zeroflow/wifi-fancontroller/modules/usr_buttons_mode.yaml

# USR Buttons Fan Control Module with Auto/Manual Mode
#
# Physical button control for fan speed using the 3 USR buttons and per-fan RGB LEDs.
# Requires Rev 3.1+ boards (which have per-fan RGB LEDs for visual feedback).
#
# Button functions (top to bottom on board):
#   USR1 (speed up): Increases selected fan speed by speed_step%. Turns fan on if off.
#                    Clamps to safety floor if stall_guard is active.
#   USR2 (select): Cycles fan selection (1→2→3→4→1). First press enters selection mode.
#                  The selected fan's LED shows that fan's current mode: magenta if it
#                  is in manual, selection_color if it is under automatic control. The
#                  other three LEDs turn off.
#   USR2 (hold ~1s): Toggles the currently selected fan between automatic
#                  temperature control and manual control. The fan stays
#                  selected and the selection window restarts, so USR1 and
#                  USR3 can set its speed right away; the LEDs return to the
#                  selection display after the confirmation flash. The
#                  toggle never changes the fan's commanded speed.
#   USR3 (speed down): Decreases selected fan speed by speed_step%. Turns fan off at 0%.
#
# Manual speed overrides persist until cleared via HA entities or the clear button.
# Selection mode auto-deactivates after override_timeout with no button presses.
#
# Coordinates with rpm_status_leds via auto_led_override global (defined in globals.yaml).
# Coordinates with temperature modules via usr_override_fan{N} globals (defined in globals.yaml).
# Respects fan{N}_safety_floor globals (defined in globals.yaml, written by stall_guard).
#
# Requires globals.yaml to be included (via hardware package or directly).
#
# SUPERSET OF usr_buttons.yaml. This module does everything usr_buttons.yaml
# does (fan selection, speed up/down, LED feedback, the four per-fan manual
# override switches) and adds the USR2 long-press mode toggle above. It
# defines the same component ids as usr_buttons.yaml. Load one or the other,
# never both.
#
# Usage:
#   packages:
#     usr_buttons_mode:
#       url: https://github.com/zeroflow/wifi-fancontroller
#       ref: main
#       files:
#         - path: modules/usr_buttons_mode.yaml
#           vars:
#             friendly_name: "My Fan Controller"
#             speed_step: "10"
#             override_timeout: "30s"
#             selection_color_r: "0"
#             selection_color_g: "0"
#             selection_color_b: "255"
# Local use (no github:// required): see /reference/standalone/
#
substitutions:
  friendly_name: "Fan Controller"
  speed_step: "10"
  override_timeout: "30s"
  selection_color_r: "0"
  selection_color_g: "0"
  selection_color_b: "255"

globals:
  - id: usr_selected_fan
    type: int
    restore_value: no
    initial_value: '0'
  # Previous button states for edge detection
  - id: usr_prev_btn1
    type: bool
    restore_value: no
    initial_value: 'false'
  - id: usr_prev_btn2
    type: bool
    restore_value: no
    initial_value: 'false'
  - id: usr_prev_btn3
    type: bool
    restore_value: no
    initial_value: 'false'
  # USR2 long-press tracking: when the press started, and whether the
  # long-press action already fired for the press currently in progress.
  - id: usr_btn2_press_start_ms
    type: uint32_t
    restore_value: no
    initial_value: '0'
  - id: usr_btn2_long_fired
    type: bool
    restore_value: no
    initial_value: 'false'
  # Snapshots the mode a fan just landed in at toggle time, so
  # usr_mode_flash reports the toggle that actually happened. Reading this
  # snapshot rather than the live usr_override_fanN flag matters because a
  # USR1 or USR3 press landing inside the flash window forces the fan to
  # manual; without the snapshot that would re-colour an in-progress flash
  # mid-sequence to report something the hold itself did not do.
  - id: usr_mode_flash_manual
    type: bool
    restore_value: no
    initial_value: 'false'
  # Persisted mirror of the shared usr_override_fanN flags (which are
  # restore_value: no in the frozen globals.yaml). These four survive a
  # reboot and are re-asserted into the live flags in the on_boot trigger
  # below, before any temperature module's first write.
  #
  # This only works because the four usr_override_sw_fanN switches below
  # carry restore_mode: DISABLED. Without it, each switch's own restore
  # fired turn_off_action during its own setup(), which zeroed both the
  # live flag and this persisted mirror before on_boot ever ran, and the
  # mode never survived a reboot at all. See the comment on those switches.
  #
  # A narrower limitation remains even with that fixed: restore_value: true
  # does not mean the write is immediate. ESPHome's preferences component
  # batches these globals and commits them to flash only on its own sync
  # interval (60s by default), not on every change. A mode change made less
  # than that interval before a power cut is still only in RAM when power is
  # lost, so the fan comes back in its previous mode. Deferred fix: have
  # usr_persist_modes call global_preferences->sync() to force an immediate
  # commit, guarded so it only fires when a mirror actually changed, since
  # USR1 and USR3 also call this script on every press and an unguarded
  # sync() would write flash on every one of those.
  - id: usr_mode_fan1
    type: bool
    restore_value: true
    initial_value: 'false'
  - id: usr_mode_fan2
    type: bool
    restore_value: true
    initial_value: 'false'
  - id: usr_mode_fan3
    type: bool
    restore_value: true
    initial_value: 'false'
  - id: usr_mode_fan4
    type: bool
    restore_value: true
    initial_value: 'false'

esphome:
  on_boot:
    - priority: -100 # Run late, after every component is set up, and well
                      # inside temperature_curve's 10s update_interval before
                      # its output sensor's first write.
      then:
        - lambda: |-
            id(usr_override_fan1) = id(usr_mode_fan1);
            id(usr_override_fan2) = id(usr_mode_fan2);
            id(usr_override_fan3) = id(usr_mode_fan3);
            id(usr_override_fan4) = id(usr_mode_fan4);
            ESP_LOGI("usr_buttons_mode", "Restored fan modes: %d %d %d %d",
              id(usr_mode_fan1), id(usr_mode_fan2),
              id(usr_mode_fan3), id(usr_mode_fan4));

script:
  - id: usr_selection_timeout
    mode: restart
    then:
      - delay: ${override_timeout}
      - lambda: |-
          // Deactivate selection mode
          id(usr_selected_fan) = 0;
          id(auto_led_override) = false;
          // Explicitly turn off all fan LEDs to prevent stale state
          auto off1 = id(fan1_led).turn_off(); off1.set_transition_length(0); off1.perform();
          auto off2 = id(fan2_led).turn_off(); off2.set_transition_length(0); off2.perform();
          auto off3 = id(fan3_led).turn_off(); off3.set_transition_length(0); off3.perform();
          auto off4 = id(fan4_led).turn_off(); off4.set_transition_length(0); off4.perform();
          ESP_LOGI("usr_buttons_mode", "Selection timeout - mode deactivated, fan LEDs cleared");

  - id: usr_update_leds
    mode: restart
    then:
      - lambda: |-
          int sel = id(usr_selected_fan);
          float r = ${selection_color_r} / 255.0f;
          float g = ${selection_color_g} / 255.0f;
          float b = ${selection_color_b} / 255.0f;
          // Turn off all fan LEDs first
          auto off1 = id(fan1_led).turn_off(); off1.set_transition_length(0); off1.perform();
          auto off2 = id(fan2_led).turn_off(); off2.set_transition_length(0); off2.perform();
          auto off3 = id(fan3_led).turn_off(); off3.set_transition_length(0); off3.perform();
          auto off4 = id(fan4_led).turn_off(); off4.set_transition_length(0); off4.perform();
          // Light up selected fan with brightness mapped to speed
          light::LightState *leds[] = {nullptr, id(fan1_led), id(fan2_led), id(fan3_led), id(fan4_led)};
          fan::Fan *fans[] = {nullptr, id(fan1), id(fan2), id(fan3), id(fan4)};
          bool modes[] = {false, id(usr_override_fan1), id(usr_override_fan2), id(usr_override_fan3), id(usr_override_fan4)};
          if (sel >= 1 && sel <= 4) {
            fan::Fan *f = fans[sel];
            float brightness = 0.2f;
            if (f->state) {
              brightness = 0.2f + (f->speed / 100.0f) * 0.8f;
            }
            if (modes[sel]) { r = 1.0f; g = 0.0f; b = 1.0f; }
            auto call = leds[sel]->turn_on();
            call.set_transition_length(0);
            call.set_rgb(r, g, b);
            call.set_brightness(brightness);
            call.set_effect("none");
            call.perform();
          }

  - id: usr_mode_flash
    mode: restart
    then:
      - lambda: 'id(auto_led_override) = true;'
      - lambda: |-
          // Magenta means manual, white means automatic. The magenta here is
          // intentionally the same colour the selection LED shows for a fan
          // already in manual, so one colour carries one meaning across both
          // indicators. Neither colour occurs in the red-to-green RPM
          // gradient rpm_status_leds paints.
          float g = id(usr_mode_flash_manual) ? 0.0f : 1.0f;
          auto c1 = id(fan1_led).turn_on(); c1.set_transition_length(0);
          c1.set_rgb(1.0, g, 1.0); c1.set_brightness(0.6); c1.set_effect("none"); c1.perform();
          auto c2 = id(fan2_led).turn_on(); c2.set_transition_length(0);
          c2.set_rgb(1.0, g, 1.0); c2.set_brightness(0.6); c2.set_effect("none"); c2.perform();
          auto c3 = id(fan3_led).turn_on(); c3.set_transition_length(0);
          c3.set_rgb(1.0, g, 1.0); c3.set_brightness(0.6); c3.set_effect("none"); c3.perform();
          auto c4 = id(fan4_led).turn_on(); c4.set_transition_length(0);
          c4.set_rgb(1.0, g, 1.0); c4.set_brightness(0.6); c4.set_effect("none"); c4.perform();
      - delay: 150ms
      - lambda: |-
          auto o1 = id(fan1_led).turn_off(); o1.set_transition_length(0); o1.perform();
          auto o2 = id(fan2_led).turn_off(); o2.set_transition_length(0); o2.perform();
          auto o3 = id(fan3_led).turn_off(); o3.set_transition_length(0); o3.perform();
          auto o4 = id(fan4_led).turn_off(); o4.set_transition_length(0); o4.perform();
      - delay: 150ms
      - lambda: |-
          float g = id(usr_mode_flash_manual) ? 0.0f : 1.0f;
          auto c1 = id(fan1_led).turn_on(); c1.set_transition_length(0);
          c1.set_rgb(1.0, g, 1.0); c1.set_brightness(0.6); c1.set_effect("none"); c1.perform();
          auto c2 = id(fan2_led).turn_on(); c2.set_transition_length(0);
          c2.set_rgb(1.0, g, 1.0); c2.set_brightness(0.6); c2.set_effect("none"); c2.perform();
          auto c3 = id(fan3_led).turn_on(); c3.set_transition_length(0);
          c3.set_rgb(1.0, g, 1.0); c3.set_brightness(0.6); c3.set_effect("none"); c3.perform();
          auto c4 = id(fan4_led).turn_on(); c4.set_transition_length(0);
          c4.set_rgb(1.0, g, 1.0); c4.set_brightness(0.6); c4.set_effect("none"); c4.perform();
      - delay: 150ms
      - lambda: |-
          auto o1 = id(fan1_led).turn_off(); o1.set_transition_length(0); o1.perform();
          auto o2 = id(fan2_led).turn_off(); o2.set_transition_length(0); o2.perform();
          auto o3 = id(fan3_led).turn_off(); o3.set_transition_length(0); o3.perform();
          auto o4 = id(fan4_led).turn_off(); o4.set_transition_length(0); o4.perform();
      - delay: 150ms
      # Terminal step: the normal path hands the LEDs to the selection
      # display so the just-toggled fan repaints in its new colour, held
      # there by the fresh override_timeout the long-press branch restarted
      # above. The guard covers the case where the selection expired while
      # this flash was running: sel is then 0, auto_led_override goes
      # false, and usr_update_leds below finds nothing selected and blanks
      # all four LEDs, the same end state the timeout already produces on
      # its own, not a stuck indicator.
      - lambda: |-
          int sel = id(usr_selected_fan);
          id(auto_led_override) = (sel >= 1 && sel <= 4);
      - script.execute: usr_update_leds

  - id: usr_persist_modes
    mode: single
    then:
      - lambda: |-
          // Mirror the live flags into their persisted twins. This is the
          // only direction that runs at runtime: live to persisted. The
          // on_boot trigger above runs the other direction, once, at boot.
          //
          // Note this only updates the in-RAM global; it does not force a
          // flash write. The preferences component commits these globals
          // to flash on its own interval (60s by default), so a power cut
          // within that narrow window after a call to this script still
          // loses the change, even though the mode otherwise survives a
          // reboot. See the comment on the usr_mode_fanN globals above for
          // the deferred fix.
          id(usr_mode_fan1) = id(usr_override_fan1);
          id(usr_mode_fan2) = id(usr_override_fan2);
          id(usr_mode_fan3) = id(usr_override_fan3);
          id(usr_mode_fan4) = id(usr_override_fan4);

# Poll buttons at 50ms for responsive edge detection
interval:
  - id: usr_button_poll
    interval: 50ms
    then:
      - lambda: |-
          bool btn1 = id(btn_usr1).state;
          bool btn2 = id(btn_usr2).state;
          bool btn3 = id(btn_usr3).state;
          bool prev1 = id(usr_prev_btn1);
          bool prev2 = id(usr_prev_btn2);
          bool prev3 = id(usr_prev_btn3);
          id(usr_prev_btn1) = btn1;
          id(usr_prev_btn2) = btn2;
          id(usr_prev_btn3) = btn3;

          // USR1 rising edge: speed up selected fan
          if (btn1 && !prev1) {
            int sel = id(usr_selected_fan);
            if (sel <= 0) return;

            int step = ${speed_step};
            int speed = 0;

            fan::Fan *fans[] = {nullptr, id(fan1), id(fan2), id(fan3), id(fan4)};
            float floors[] = {0, id(fan1_safety_floor), id(fan2_safety_floor), id(fan3_safety_floor), id(fan4_safety_floor)};
            bool *overrides[] = {nullptr, &id(usr_override_fan1), &id(usr_override_fan2), &id(usr_override_fan3), &id(usr_override_fan4)};

            fan::Fan *f = fans[sel];
            float floor_val = floors[sel];

            if (f->state) {
              speed = f->speed + step;
            } else {
              speed = step;
            }
            if (speed > 100) speed = 100;
            int floor_int = (int)ceil(floor_val);
            if (floor_val > 0 && speed > 0 && speed < floor_int) speed = floor_int;

            auto call = f->turn_on();
            call.set_speed(speed);
            call.perform();
            *overrides[sel] = true;
            id(usr_persist_modes).execute();

            id(usr_update_leds).execute();
            id(usr_selection_timeout).execute();
            ESP_LOGI("usr_buttons_mode", "USR1: fan %d speed -> %d%%", sel, speed);
          }

          // USR2: three-part state machine that disambiguates a short press
          // (cycle fan selection, fires on release) from a long press (toggle
          // the selected fan's auto/manual mode, fires while still held).
          const uint32_t USR_LONG_PRESS_MS = 1000;

          // Rising edge: start timing. Take no other action -- a press is
          // only known to be short once it comes back up.
          if (btn2 && !prev2) {
            id(usr_btn2_press_start_ms) = millis();
            id(usr_btn2_long_fired) = false;
          }

          // Held: fire the long-press toggle the instant the threshold is
          // crossed, while the button is still down.
          if (btn2 && prev2) {
            if (!id(usr_btn2_long_fired)) {
              uint32_t elapsed = millis() - id(usr_btn2_press_start_ms);
              if (elapsed >= USR_LONG_PRESS_MS) {
                int sel = id(usr_selected_fan);
                if (sel >= 1 && sel <= 4) {
                  id(usr_btn2_long_fired) = true;

                  bool *overrides[] = {nullptr, &id(usr_override_fan1), &id(usr_override_fan2), &id(usr_override_fan3), &id(usr_override_fan4)};
                  *overrides[sel] = !*overrides[sel];
                  id(usr_persist_modes).execute();
                  ESP_LOGI("usr_buttons_mode", "USR2 long-press: fan %d mode -> %s", sel, *overrides[sel] ? "manual" : "auto");

                  // Keep the fan selected through the toggle so its speed
                  // can be set with USR1 and USR3 right away, with no
                  // second USR2 press needed. Rearm the pending timeout to
                  // a fresh full override_timeout rather than cancelling
                  // it: usr_selection_timeout is mode: restart, so calling
                  // execute() again restarts the delay from zero instead
                  // of stacking a second run.
                  id(usr_selection_timeout).execute();
                  id(usr_mode_flash_manual) = *overrides[sel];
                  id(usr_mode_flash).execute();
                }
              }
            }
          }

          // Falling edge: only a short press if the long-press action never
          // fired for this press. Clear the latch unconditionally so it can
          // never leak into the next press.
          if (!btn2 && prev2) {
            if (!id(usr_btn2_long_fired)) {
              int sel = id(usr_selected_fan);
              sel = (sel <= 0 || sel >= 4) ? 1 : sel + 1;
              id(usr_selected_fan) = sel;
              id(auto_led_override) = true;
              id(usr_update_leds).execute();
              id(usr_selection_timeout).execute();
              ESP_LOGI("usr_buttons_mode", "USR2: fan %d selected", sel);
            }
            id(usr_btn2_long_fired) = false;
          }

          // USR3 rising edge: speed down selected fan
          if (btn3 && !prev3) {
            int sel = id(usr_selected_fan);
            if (sel <= 0) return;

            int step = ${speed_step};

            fan::Fan *fans[] = {nullptr, id(fan1), id(fan2), id(fan3), id(fan4)};
            float floors[] = {0, id(fan1_safety_floor), id(fan2_safety_floor), id(fan3_safety_floor), id(fan4_safety_floor)};
            bool *overrides[] = {nullptr, &id(usr_override_fan1), &id(usr_override_fan2), &id(usr_override_fan3), &id(usr_override_fan4)};

            fan::Fan *f = fans[sel];
            float floor_val = floors[sel];
            int floor_int = (int)ceil(floor_val);
            int speed = f->state ? (f->speed - step) : 0;

            // If speed would be below safety floor, snap to off
            if (speed > 0 && floor_val > 0 && speed < floor_int) speed = 0;

            if (speed <= 0) {
              auto call = f->turn_off();
              call.perform();
              speed = 0;
            } else {
              auto call = f->turn_on();
              call.set_speed(speed);
              call.perform();
            }
            *overrides[sel] = true;
            id(usr_persist_modes).execute();

            id(usr_update_leds).execute();
            id(usr_selection_timeout).execute();
            ESP_LOGI("usr_buttons_mode", "USR3: fan %d speed -> %d%%", sel, speed);
          }

button:
  - platform: template
    name: "${friendly_name} Clear Fan Overrides"
    id: usr_clear_overrides
    icon: mdi:fan-off
    entity_category: config
    on_press:
      - lambda: |-
          id(usr_override_fan1) = false;
          id(usr_override_fan2) = false;
          id(usr_override_fan3) = false;
          id(usr_override_fan4) = false;
          ESP_LOGI("usr_buttons_mode", "All manual fan overrides cleared");
      - script.execute: usr_persist_modes

switch:
  # restore_mode: DISABLED on all four switches below is load-bearing, not
  # cosmetic. The default restore_mode is ALWAYS_OFF, and a template switch's
  # setup() calls get_initial_state_with_restore_mode(), which returns a
  # value for every mode except DISABLED. For ALWAYS_OFF that value is
  # false, so setup() called turn_off(), which fired turn_off_action on
  # every boot, before the module's own on_boot restore (priority -100, last)
  # ever ran. turn_off_action sets id(usr_override_fanN) = false and calls
  # usr_persist_modes, which then mirrors that false into usr_mode_fanN,
  # wiping the persisted mode too. The mode never survived a reboot as a
  # result. With DISABLED, get_initial_state_with_restore_mode() returns an
  # empty optional, setup() takes no action, and the switch simply reflects
  # whatever id(usr_override_fanN) already holds, which by then is the value
  # on_boot restored.
  - platform: template
    name: "${friendly_name} Fan 1 Manual Override"
    id: usr_override_sw_fan1
    icon: mdi:fan-clock
    entity_category: config
    restore_mode: DISABLED
    lambda: |-
      return id(usr_override_fan1);
    turn_on_action:
      - lambda: |-
          id(usr_override_fan1) = true;
      - script.execute: usr_persist_modes
    turn_off_action:
      - lambda: |-
          id(usr_override_fan1) = false;
      - script.execute: usr_persist_modes

  - platform: template
    name: "${friendly_name} Fan 2 Manual Override"
    id: usr_override_sw_fan2
    icon: mdi:fan-clock
    entity_category: config
    restore_mode: DISABLED
    lambda: |-
      return id(usr_override_fan2);
    turn_on_action:
      - lambda: |-
          id(usr_override_fan2) = true;
      - script.execute: usr_persist_modes
    turn_off_action:
      - lambda: |-
          id(usr_override_fan2) = false;
      - script.execute: usr_persist_modes

  - platform: template
    name: "${friendly_name} Fan 3 Manual Override"
    id: usr_override_sw_fan3
    icon: mdi:fan-clock
    entity_category: config
    restore_mode: DISABLED
    lambda: |-
      return id(usr_override_fan3);
    turn_on_action:
      - lambda: |-
          id(usr_override_fan3) = true;
      - script.execute: usr_persist_modes
    turn_off_action:
      - lambda: |-
          id(usr_override_fan3) = false;
      - script.execute: usr_persist_modes

  - platform: template
    name: "${friendly_name} Fan 4 Manual Override"
    id: usr_override_sw_fan4
    icon: mdi:fan-clock
    entity_category: config
    restore_mode: DISABLED
    lambda: |-
      return id(usr_override_fan4);
    turn_on_action:
      - lambda: |-
          id(usr_override_fan4) = true;
      - script.execute: usr_persist_modes
    turn_off_action:
      - lambda: |-
          id(usr_override_fan4) = false;
      - script.execute: usr_persist_modes
